Forairaaaaa/Peak-T2/2.Firmware/PlatformIO/Peak_ESP32_X-Track_fw_T2.0/src/HAL/HAL_AHRS.cpp

#if 0
#include "HAL.h"
extern "C" {
#include <math.h>
}

static void MahonyAHRSupdate(
    float gx, float gy, float gz,
    float ax, float ay, float az,
    float mx, float my, float mz)
{
    const static float sampleFreq = 0.002;
    const static float twoKp = 10;
    const static float twoKi = 0;
    static float q0 = 0, q1 = 0, q2 = 0, q3 = 0;
    float recipNorm;
    float q0q0, q0q1, q0q2, q0q3, q1q1, q1q2, q1q3, q2q2, q2q3, q3q3;
    float hx, hy, bx, bz;
    float halfvx, halfvy, halfvz, halfwx, halfwy, halfwz;
    float halfex, halfey, halfez;
    float qa, qb, qc;

    // Compute feedback only if accelerometer measurement valid (avoids NaN in accelerometer normalisation)

    if (!((ax == 0.0f) && (ay == 0.0f) && (az == 0.0f)))
    {
        // Normalise accelerometer measurement

        recipNorm = sqrt(ax * ax + ay * ay + az * az);

        ax *= recipNorm;
        ay *= recipNorm;
        az *= recipNorm;

        // Normalise magnetometer measurement

        recipNorm = sqrt(mx * mx + my * my + mz * mz);
        mx *= recipNorm;
        my *= recipNorm;
        mz *= recipNorm;

        // Auxiliary variables to avoid repeated arithmetic

        q0q0 = q0 * q0;
        q0q1 = q0 * q1;
        q0q2 = q0 * q2;
        q0q3 = q0 * q3;
        q1q1 = q1 * q1;
        q1q2 = q1 * q2;
        q1q3 = q1 * q3;
        q2q2 = q2 * q2;
        q2q3 = q2 * q3;
        q3q3 = q3 * q3;

        // Reference direction of Earth��s magnetic field

        hx = 2.0f * (mx * (0.5f - q2q2 - q3q3) + my * (q1q2 - q0q3) + mz * (q1q3 + q0q2));
        hy = 2.0f * (mx * (q1q2 + q0q3) + my * (0.5f - q1q1 - q3q3) + mz * (q2q3 - q0q1));
        bx = sqrt(hx * hx + hy * hy);
        bz = 2.0f * (mx * (q1q3 - q0q2) + my * (q2q3 + q0q1) + mz * (0.5f - q1q1 - q2q2));

        // Estimated direction of gravity and magnetic field

        halfvx = q1q3 - q0q2;
        halfvy = q0q1 + q2q3;
        halfvz = q0q0 - 0.5f + q3q3;
        halfwx = bx * (0.5f - q2q2 - q3q3) + bz * (q1q3 - q0q2);
        halfwy = bx * (q1q2 - q0q3) + bz * (q0q1 + q2q3);
        halfwz = bx * (q0q2 + q1q3) + bz * (0.5f - q1q1 - q2q2);

        // Error is sum of cross product between estimated direction and measured direction of field vectors

        halfex = (ay * halfvz - az * halfvy) + (my * halfwz - mz * halfwy);
        halfey = (az * halfvx - ax * halfvz) + (mz * halfwx - mx * halfwz);
        halfez = (ax * halfvy - ay * halfvx) + (mx * halfwy - my * halfwx);
        // Compute and apply integral feedback if enabled

        static float integralFBx = 0, integralFBy = 0, integralFBz = 0;

        if (twoKi > 0.0f)
        {
            integralFBx += twoKi * halfex * (1.0f / sampleFreq); // integral error scaled by Ki
            integralFBy += twoKi * halfey * (1.0f / sampleFreq);
            integralFBz += twoKi * halfez * (1.0f / sampleFreq);
            gx += integralFBx; // apply integral feedback
            gy += integralFBy;
            gz += integralFBz;
        }
        else
        {
            integralFBx = 0.0f; // prevent integral windup
            integralFBy = 0.0f;
            integralFBz = 0.0f;
        }

        // Apply proportional feedback

        gx += twoKp * halfex;
        gy += twoKp * halfey;
        gz += twoKp * halfez;

    }

    // Integrate rate of change of quaternion

    gx *= (0.5f * (1.0f / sampleFreq)); // pre-multiply common factors
    gy *= (0.5f * (1.0f / sampleFreq));
    gz *= (0.5f * (1.0f / sampleFreq));

    qa = q0;
    qb = q1;
    qc = q2;

    q0 += (-qb * gx - qc * gy - q3 * gz);
    q1 += (qa * gx + qc * gz - q3 * gy);
    q2 += (qa * gy - qb * gz + q3 * gx);
    q3 += (qa * gz + qb * gy - qc * gx);

    // Normalise quaternion

    recipNorm = sqrt(q0 * q0 + q1 * q1 + q2 * q2 + q3 * q3);

    q0 *= recipNorm;
    q1 *= recipNorm;
    q2 *= recipNorm;
    q3 *= recipNorm;
}

void HAL::AHRS_Update()
{
}

#endif
