Forairaaaaa/Peak-T2/2.Firmware/PlatformIO/Peak-T2.0_Arduino-fw/src/HAL/HAL_Clock.cpp

#include "HAL.h"
// #include "rtc.h"

void HAL::Clock_Init()
{
    // RTC_Init();

    Clock_Info_t info;
    Clock_GetInfo(&info);
    Serial.printf(
        "Clock: %04d-%02d-%02d %s %02d:%02d:%02d\r\n",
        info.year,
        info.month,
        info.day,
        Clock_GetWeekString(info.week),
        info.hour,
        info.minute,
        info.second
    );
}

void HAL::Clock_GetInfo(Clock_Info_t* info)
{
    info->year = gps.date.year();
    info->month = gps.date.month();
    info->day = gps.date.day();
    info->week = 1;
    info->hour = gps.time.hour();
    info->minute = gps.time.minute();
    info->second = gps.time.second();
    info->millisecond = 0;
}

void HAL::Clock_SetInfo(const Clock_Info_t* info)
{
    // RTC_SetTime(
    //     info->year,
    //     info->month,
    //     info->day,
    //     info->hour,
    //     info->minute,
    //     info->second
    // );
}

const char* HAL::Clock_GetWeekString(uint8_t week)
{
    const char* week_str[] = {"SUN", "MON", "TUE", "WED", "THU", "FRI", "SAT"};
    return week < 7 ? week_str[week] : "";
}
