Forairaaaaa/Peak-T2/2.Firmware/PlatformIO/Peak-T2.0_Arduino-fw/src/HAL/HAL_Display.cpp

#include "HAL.h"

TFT_eSPI tft = TFT_eSPI();


void HAL::Display_Init()
{
    /* LCD init */
    tft.init();
    tft.setRotation(0);
    tft.fillScreen(TFT_BLACK);

    Serial.println("LCD: initialized");
}
