Forairaaaaa/Peak-T2/2.Firmware/PlatformIO/Peak-T2.0_Arduino-fw/src/HAL/HAL_IMU.cpp

#include "HAL.h"
// #include "LSM6DSM/LSM6DSM.h"

// static LSM6DSM imu;
static HAL::CommitFunc_t CommitFunc = nullptr;
static void* UserData = nullptr;

bool HAL::IMU_Init()
{
    Serial.print("IMU: init...");

    // bool success = imu.Init();
    bool success = false;

    Serial.println(success ? "success" : "failed");

    return success;
}

void HAL::IMU_SetCommitCallback(CommitFunc_t func, void* userData)
{
    CommitFunc = func;
    UserData = userData;
}

void HAL::IMU_Update()
{
    // IMU_Info_t imuInfo;
    // imu.GetMotion6(
    //     &imuInfo.ax, &imuInfo.ay, &imuInfo.az,
    //     &imuInfo.gx, &imuInfo.gy, &imuInfo.gz
    // );

    // imuInfo.ax = 0;
    // imuInfo.ay = 0;
    // imuInfo.az = 0;
    // imuInfo.gx = 0;
    // imuInfo.gy = 0;
    // imuInfo.gz = 0;

//    Serial.printf(
//        "ax = %d, ay = %d, az = %d, gx = %d, gy = %d, gz = %d\r\n",
//        imuInfo.ax, imuInfo.ay, imuInfo.az, imuInfo.gx, imuInfo.gy, imuInfo.gz
//    );

    // imuInfo.steps = imu.GetCurrentStep();
    // imuInfo.steps = 0;

    // if(CommitFunc)
    // {
    //     CommitFunc(&imuInfo, UserData);
    // }
    // Serial.println("IMU: hi");
}
